hackerwarehouse/HW-DC26-Badge/src/HW-DC26-Badge/wifi-client.h

#ifndef HW_WIFICLIENT_H
#define HW_WIFICLIENT_H

void ConnectInternet();
void GoogleAuth();
void IPConfig();
void NTPdisplay();
void NTPstart();
void NTPstop();
void NTPupdate();
void HTTPSysUpdate();

#endif
