hackerwarehouse/HW-DC26-Badge/src/HW-DC26-Badge/wifi-pkt1.h

#ifndef HW_PKT1_H
#define HW_PKT1_H

void Pkt_Monitor();   // remix of https://github.com/spacehuhn/PacketMonitor32
//void DeauthMonitor();  // remix of https://github.com/spacehuhn/DeauthDetector
//void DeauthDetect();
void RickRollSSID(); // remix of https://github.com/Jeija/esp32-80211-tx

#endif
